bensmith87/gauge/sketch/Trip.h

#include "Mode.h"
#include "Gps.h"

class Trip : public Mode {
  Gps* gps;
  
public:
  Trip(Gps* newGps) : Mode("TRIP") {
    gps = newGps;
  }

  void update() {
    char tripText[5];
    sprintf(tripText, "%5.1f", gps->getTrip() / 1000);
    setValue(tripText);
  }

  boolean handlePress(boolean longPress) {
    if (longPress) {
      gps->resetTrip();
      return true;
    }
    
    return false;
  }
};
