bensmith87/gauge/sketch/Battery.h

#include "Mode.h"

#define BATTERY_PIN A2
#define R1 4700
#define R2 10000

class Battery : public Mode {
  
public:
  Battery() : Mode("BATT") { }

  void update() {
    double voltage = analogRead(BATTERY_PIN) / 1024.0 * 3.3 * (R1 + R2) / R2;
    char battText[5];
    sprintf(battText, "%4.1fV", voltage);
    setValue(battText);
  }
};
